payano/zigbee_LED_project/Src/Mrf24j.cpp

/**
 * mrf24j.cpp, Karl Palsson, 2011, karlp@tweak.net.au
 * modified bsd license / apache license
 */

#include "Mrf24j.h"
#include <string.h>
//#include "stm32f3xx_hal_spi.h"

// aMaxPHYPacketSize = 127, from the 802.15.4-2006 standard.
static uint8_t rx_buf[127];

// essential for obtaining the data frame only
// bytes_MHR = 2 Frame control + 1 sequence number + 2 panid + 2 shortAddr Destination + 2 shortAddr Source
static int bytes_MHR = 9;
static int bytes_FCS = 2; // FCS length = 2
static int bytes_nodata = bytes_MHR + bytes_FCS; // no_data bytes in PHY payload,  header length + FCS

static int ignoreBytes = 0; // bytes to ignore, some modules behaviour.

static boolean bufPHY = false; // flag to buffer all bytes in PHY Payload, or not
//static boolean bufPHY = true; // flag to buffer all bytes in PHY Payload, or not

volatile uint8_t flag_got_rx;
volatile uint8_t flag_got_tx;

static rx_info_t rx_info;
static tx_info_t tx_info;


/**
 * Constructor MRF24J Object.
 * @param pin_reset, @param pin_chip_select, @param pin_interrupt
 */
Mrf24j::Mrf24j(SPI_HandleTypeDef* spi,gpio_pin* pin_reset, gpio_pin* pin_chip_select, gpio_pin* pin_interrupt):
      spi(spi),
      pin_reset(pin_reset),
      pin_cs(pin_chip_select),
      pin_int(pin_interrupt)
{

  HAL_GPIO_WritePin(SPI_CS_GPIO_Port, SPI_CS_Pin, GPIO_PIN_SET);
}

void Mrf24j::reset(void) {
  // I cant reset the mrf.... PCB does not have a pin for that!
//  HAL_GPIO_WritePin(pin_reset->port, pin_reset->pin, GPIO_PIN_RESET);
//  HAL_Delay(100);
//  HAL_GPIO_WritePin(pin_reset->port, pin_reset->pin, GPIO_PIN_SET);
//  HAL_Delay(200);
}

byte Mrf24j::read_short(byte address) {

  HAL_GPIO_WritePin(SPI_CS_GPIO_Port, SPI_CS_Pin, GPIO_PIN_RESET);

  address = address<<1 & 0b01111110;
  HAL_SPI_Transmit(spi, &address, 1,1);

  byte ret = 0x0;
  byte bogus = 0x00;
  HAL_SPI_TransmitReceive(spi, &bogus, &ret, 1, 1);
//  HAL_SPI_Receive(spi, &ret,1,1);

  HAL_GPIO_WritePin(SPI_CS_GPIO_Port, SPI_CS_Pin, GPIO_PIN_SET);

  return ret;
}

byte Mrf24j::read_long(word address) {
  HAL_GPIO_WritePin(SPI_CS_GPIO_Port, SPI_CS_Pin, GPIO_PIN_RESET);

  byte ahigh = 0x80 | (address >> 3);
  byte alow = address << 5;

  HAL_SPI_Transmit(spi, &ahigh, 1,1);
  HAL_SPI_Transmit(spi, &alow, 1,1);

  byte ret;
  byte bogus = 0x00;
  HAL_SPI_TransmitReceive(spi, &bogus, &ret, 1, 1);
  //HAL_SPI_Receive(spi, &ret,1,1);

  HAL_GPIO_WritePin(SPI_CS_GPIO_Port, SPI_CS_Pin, GPIO_PIN_SET);

  return ret;
}


void Mrf24j::write_short(byte address, byte data) {
  HAL_GPIO_WritePin(SPI_CS_GPIO_Port, SPI_CS_Pin, GPIO_PIN_RESET);

  address = (address<<1 & 0b01111110) | 0x01;
  HAL_SPI_Transmit(spi, &address, 1,1);
  HAL_SPI_Transmit(spi, &data, 1,1);

  HAL_GPIO_WritePin(SPI_CS_GPIO_Port, SPI_CS_Pin, GPIO_PIN_SET);

}

void Mrf24j::write_long(word address, byte data) {
  HAL_GPIO_WritePin(SPI_CS_GPIO_Port, SPI_CS_Pin, GPIO_PIN_RESET);

  byte ahigh = 0x80 | (address >> 3);
  byte alow = (address << 5) | 0x10;

  HAL_SPI_Transmit(spi, &ahigh, 1,1);
  HAL_SPI_Transmit(spi, &alow, 1,1);

  HAL_SPI_Transmit(spi, &data, 1,1);

  HAL_GPIO_WritePin(SPI_CS_GPIO_Port, SPI_CS_Pin, GPIO_PIN_SET);

}

word Mrf24j::get_pan(void) {
  byte panh = read_short(MRF_PANIDH);
  return (panh << 8) | read_short(MRF_PANIDL);
}

void Mrf24j::set_pan(word panid) {
  write_short(MRF_PANIDH, panid >> 8);
  write_short(MRF_PANIDL, panid & 0xff);
}

void Mrf24j::address16_write(word address16) {
  write_short(MRF_SADRH, address16 >> 8);
  write_short(MRF_SADRL, address16 & 0xff);
}

word Mrf24j::address16_read(void) {
  byte a16h = read_short(MRF_SADRH);
  return a16h << 8 | read_short(MRF_SADRL);
}

/**
 * Simple send 16, with acks, not much of anything.. assumes src16 and local pan only.
 * @param data
 */
void Mrf24j::send16(word dest16, const char * data, byte len) {
  //byte len = strlen(data); // get the length of the char* array
  int i = 0;
  write_long(i++, bytes_MHR); // header length
  // +ignoreBytes is because some module seems to ignore 2 bytes after the header?!.
  // default: ignoreBytes = 0;
  write_long(i++, bytes_MHR+ignoreBytes+len);

  // 0 | pan compression | ack | no security | no data pending | data frame[3 bits]
  write_long(i++, 0b01100001); // first byte of Frame Control
  // 16 bit source, 802.15.4 (2003), 16 bit dest,
  write_long(i++, 0b10001000); // second byte of frame control
  write_long(i++, 1);  // sequence number 1

  word panid = get_pan();

  write_long(i++, panid & 0xff);  // dest panid
  write_long(i++, panid >> 8);
  write_long(i++, dest16 & 0xff);  // dest16 low
  write_long(i++, dest16 >> 8); // dest16 high

  word src16 = address16_read();
  write_long(i++, src16 & 0xff); // src16 low
  write_long(i++, src16 >> 8); // src16 high

  // All testing seems to indicate that the next two bytes are ignored.
  //2 bytes on FCS appended by TXMAC
  i+=ignoreBytes;
  for (int q = 0; q < len; q++) {
    write_long(i++, data[q]);
  }
  // ack on, and go!
  write_short(MRF_TXNCON, (1<<MRF_TXNACKREQ | 1<<MRF_TXNTRIG));

  //byte len = strlen(data); // get the length of the char* array
//  int i = 0;
//  write_long(i++, bytes_MHR); // header length
//  // +ignoreBytes is because some module seems to ignore 2 bytes after the header?!.
//  // default: ignoreBytes = 0;
//
//
//  //bytes_MHR = 2 Frame control + 1 sequence number + 2 panid + 8 shortAddr Destination + 8 shortAddr Source
//  bytes_MHR = 15;
//  write_long(i++, bytes_MHR+ignoreBytes+len);
//
//  // 0 | pan compression | ack | no security | no data pending | data frame[3 bits]
//  write_long(i++, 0x61); // first byte of Frame Control
//  // 16 bit source, 802.15.4 (2003), 16 bit dest,
//  write_long(i++, 0x8c); // second byte of frame control
//  write_long(i++, 1);  // sequence number 1
//
//  word panid = get_pan();
//
//  write_long(i++, panid & 0xff);  // dest panid
//  write_long(i++, panid >> 8);
//
//  // Dest
//  write_long(i++, 0x57);
//  write_long(i++, 0xeb);
//  write_long(i++, 0x1c);
//  write_long(i++, 0xe4);
//  write_long(i++, 0xd6);
//  write_long(i++, 0x2c);
//  write_long(i++, 0x55);
//  write_long(i++, 0xd6);
//  //write_long(i++, dest16 & 0xff);  // dest16 low
//  //write_long(i++, dest16 >> 8); // dest16 high
//
//  // Source
//  word src16 = address16_read();
//  write_long(i++, 0xb2);
//  write_long(i++, 0x94);
//
//
//  //write_long(i++, src16 & 0xff); // src16 low
//  //write_long(i++, src16 >> 8); // src16 high
//
//  // All testing seems to indicate that the next two bytes are ignored.
//  //2 bytes on FCS appended by TXMAC
//  i+=ignoreBytes;
//  for (int q = 0; q < len; q++) {
//    write_long(i++, data[q]);
//  }
//  // ack on, and go!
//  write_short(MRF_TXNCON, (1<<MRF_TXNACKREQ | 1<<MRF_TXNTRIG));
}

void Mrf24j::set_interrupts(void) {
  // interrupts for rx and tx normal complete
  write_short(MRF_INTCON, 0b11110110);
}

/** use the 802.15.4 channel numbers..
 */
void Mrf24j::set_channel(byte channel) {
  //  (((channel - 11) << 4) | 0x03));
  write_long(MRF_RFCON0, (((channel - 11) << 4) | 0x03));
}

byte Mrf24j::get_channel() {
  byte ret = read_long(MRF_RFCON0);
  ret = (ret >> 4) + 1 ;
  return ret;
}

void Mrf24j::init(void) {

  // Seems a bit ridiculous when I use reset pin anyway
  write_short(MRF_SOFTRST, 0x7); // from manual
  while ((read_short(MRF_SOFTRST) & 0x7) != 0) {
    ; // wait for soft reset to finish
  }

  write_short(MRF_PACON2, 0x98); // – Initialize FIFOEN = 1 and TXONTS = 0x6.
  write_short(MRF_TXSTBL, 0x95); // – Initialize RFSTBL = 0x9.

  write_long(MRF_RFCON0, 0x03); // – Initialize RFOPT = 0x03.
  write_long(MRF_RFCON1, 0x01); // – Initialize VCOOPT = 0x02.
  write_long(MRF_RFCON2, 0x80); // – Enable PLL (PLLEN = 1).
  write_long(MRF_RFCON6, 0x90); // – Initialize TXFIL = 1 and 20MRECVR = 1.
  write_long(MRF_RFCON7, 0x80); // – Initialize SLPCLKSEL = 0x2 (100 kHz Internal oscillator).
  write_long(MRF_RFCON8, 0x10); // – Initialize RFVCO = 1.
  write_long(MRF_SLPCON1, 0x21); // – Initialize CLKOUTEN = 1 and SLPCLKDIV = 0x01.

  //  Configuration for nonbeacon-enabled devices (see Section 3.8 “Beacon-Enabled and
  //  Nonbeacon-Enabled Networks”):
  write_short(MRF_BBREG2, 0x80); // Set CCA mode to ED
  write_short(MRF_CCAEDTH, 0x60); // – Set CCA ED threshold.
  write_short(MRF_BBREG6, 0x40); // – Set appended RSSI value to RXFIFO.
  set_interrupts();
  //
  set_channel(11);
  // max power is by default.. just leave it...
  // Set transmitter power - See “REGISTER 2-62: RF CONTROL 3 REGISTER (ADDRESS: 0x203)”.
  write_short(MRF_RFCTL, 0x04); //  – Reset RF state machine.
  write_short(MRF_RFCTL, 0x00); // part 2
  //delay(1); // delay at least 192usec

  HAL_Delay(250);

}

/**
 * Call this from within an interrupt handler connected to the MRFs output
 * interrupt pin.  It handles reading in any data from the module, and letting it
 * continue working.
 * Only the most recent data is ever kept.
 */
void Mrf24j::interrupt_handler(void) {
  memset(rx_buf,0,127);
  memset(rx_info.rx_data,0,116);
  uint8_t last_interrupt = read_short(MRF_INTSTAT);
  if (last_interrupt & MRF_I_RXIF) {
    flag_got_rx++;
    // read out the packet data...
    //noInterrupts();
    rx_disable();
    // read start of rxfifo for, has 2 bytes more added by FCS. frame_length = m + n + 2
    uint8_t frame_length = read_long(0x300);

    // buffer all bytes in PHY Payload
    if(bufPHY){
      int rb_ptr = 0;
      for (int i = 0; i < frame_length; i++) { // from 0x301 to (0x301 + frame_length -1)
        rx_buf[rb_ptr++] = read_long(0x301 + i);
      }
    }

    // buffer data bytes
    int rd_ptr = 0;
    // from (0x301 + bytes_MHR) to (0x301 + frame_length - bytes_nodata - 1)
    auto const dataLength = rx_datalength();
    for (int i = 9; i < frame_length-2; i++) {
      rx_info.rx_data[rd_ptr++] = read_long(0x301 + i);
    }

    rx_info.frame_length = frame_length;
    // same as datasheet 0x301 + (m + n + 2) <-- frame_length
    rx_info.lqi = read_long(0x301 + frame_length);
    // same as datasheet 0x301 + (m + n + 3) <-- frame_length + 1
    rx_info.rssi = read_long(0x301 + frame_length + 1);

//    HAL_Delay(1);
    rx_enable();
    //interrupts();
  }
  if (last_interrupt & MRF_I_TXNIF) {
    flag_got_tx++;
    uint8_t tmp = read_short(MRF_TXSTAT);
    // 1 means it failed, we want 1 to mean it worked.
    tx_info.tx_ok = !(tmp & ~(1 << TXNSTAT));
    tx_info.retries = tmp >> 6;
    tx_info.channel_busy = (tmp & (1 << CCAFAIL));
  }
}


/**
 * Call this function periodically, it will invoke your nominated handlers
 */
void Mrf24j::check_flags(void (*rx_handler)(void), void (*tx_handler)(void)){
  // TODO - we could check whether the flags are > 1 here, indicating data was lost?
  if (flag_got_rx) {
    flag_got_rx = 0;
    rx_handler();
  }
  if (flag_got_tx) {
    flag_got_tx = 0;
    tx_handler();
  }
}

/**
 * Set RX mode to promiscuous, or normal
 */
void Mrf24j::set_promiscuous(boolean enabled) {
  if (enabled) {
    write_short(MRF_RXMCR, 0x01);
  } else {
    write_short(MRF_RXMCR, 0x00);
  }
}

rx_info_t * Mrf24j::get_rxinfo(void) {
  return &rx_info;
}

tx_info_t * Mrf24j::get_txinfo(void) {
  return &tx_info;
}

uint8_t * Mrf24j::get_rxbuf(void) {
  return rx_buf;
}

int Mrf24j::rx_datalength(void) {
  return rx_info.frame_length - bytes_nodata;
}

void Mrf24j::set_ignoreBytes(int ib) {
  // some modules behaviour
  ignoreBytes = ib;
}

/**
 * Set bufPHY flag to buffer all bytes in PHY Payload, or not
 */
void Mrf24j::set_bufferPHY(boolean bp) {
  bufPHY = bp;
}

boolean Mrf24j::get_bufferPHY(void) {
  return bufPHY;
}

/**
 * Set PA/LNA external control
 */
void Mrf24j::set_palna(boolean enabled) {
  if (enabled) {
    write_long(MRF_TESTMODE, 0x07); // Enable PA/LNA on MRF24J40MB module.
  }else{
    write_long(MRF_TESTMODE, 0x00); // Disable PA/LNA on MRF24J40MB module.
  }
}

void Mrf24j::rx_flush(void) {
  write_short(MRF_RXFLUSH, 0x01);
}

void Mrf24j::rx_disable(void) {
  write_short(MRF_BBREG1, 0x04);  // RXDECINV - disable receiver
}

void Mrf24j::rx_enable(void) {
  write_short(MRF_BBREG1, 0x00);  // RXDECINV - enable receiver
}
