payano/zigbee_LED_project/Src/InterruptHandler.h

/*
 * InterruptHandler.h
 *
 *  Created on: Sep 25, 2017
 *      Author: johan
 */

#pragma once
#include "IHandler.h"

constexpr int INTERRUPT_LENGTH = 3;

class InterruptHandler: public IHandler {
private:
  IHandler* mRecipients[HandlerName::SIZE];
  static bool sInterrupted[HandlerName::SIZE]; //static
  uint32_t* mAdcBuffer;
  uint32_t mAdcBufferLen;

public:
  InterruptHandler();
  virtual ~InterruptHandler();

  //static void putInterruptData(uint32_t InterruptIncData[3]);
  void addAdcBuffer(uint32_t* buffer, int len);

  void addMessage(Message* message) override;
  void run() override;
  void setInterrupted() override;
  static void setInterrupted(HandlerName handler);
  bool getInterrupted() override;
  void addRecipient(IHandler* recipient, HandlerName recipientName) override;
};
